3s1d/tweety/src/piezo.h

/*
 * piezo.h
 *
 *  Created on: Jul 30, 2016
 *      Author: sid
 */

#ifndef PIEZO_H_
#define PIEZO_H_

#define PIEZO_PIN		B,1

#define PIEZO_SINK_EEPROM	0
#define MINTONELENGTH		200

#define BEEP_ON			1
#define BEEP_OFF		0
#define BEEP_NOCHANGE		-1


/* 3.3mH coil -> tau = 79uS */
/* do not succeed 150uS (2tau) charge time */

/* charge time in uS */
#define PIEZO_VOL		((F_CPU/1000000UL) * 150)

extern uint8_t p_dosink;

void p_init(void);
void p_config(void);

/* control piezo, freq in Hz, approx. [100,3000], avoid 0 !! */
void p_set(uint16_t freq);
void p_off(void);

/* turn on/off signals */
void p_hello(void);
void p_bye(void);

void p_beep(uint8_t n);
void p_climb(void);

#endif /* PIEZO_H_ */
