3s1d/tweety/src/sleep.c

/*
 * sleep.c
 *
 *  Created on: Aug 2, 2016
 *      Author: sid
 */

#include <avr/io.h>
#include <avr/interrupt.h>
#include <avr/sleep.h>
#include <util/delay.h>

#include "flexport.h"
#include "battery.h"
#include "button.h"
#include "climb.h"
#include "piezo.h"
#include "sleep.h"

#include "debug.h"


ISR(PCINT2_vect)
{

}

void sleep(void)
{
	/* prepare system */
	climb_deinit();
	_delay_ms(250);

	p_bye();

	/* wait for button released */
	while(btn_pressed());

	/* configure button to trigger an PC interrupt (PCINT18 @ D,2) */
	PCMSK2 = _BV(PCINT18);
	PCICR = _BV(PCIE2);

	//uint8_t d = 10;
	//debug_put(&d, 1);

	set_sleep_mode(SLEEP_MODE_PWR_DOWN);
	uint8_t sleep = 1;
	while(sleep)
	{
		/* sleep */
		sleep_mode();

		/* switch de-bounce */
		_delay_ms(100);

		/* minimal button press time 1.5sec */
		uint8_t i;
		for(i=0; i<140; i++)
		{
			/* way too short */
			if(!btn_pressed())
			{
				i = 255;
				break;
			}
			_delay_ms(10);
		}
		if(i == 255)
			continue;

		//d = 13;
		//debug_put(&d, 1);

		/* quickly indicate we are up and running */
		//note: longer beeps confuses me...
		p_set(1000);
		_delay_ms(100);
		p_off();
		_delay_ms(100);

		for(i=0; i < 10; i++)
		{
			/* button released in time -> power on */
			if(!btn_pressed())
			{
				sleep = 0;
				break;
			}
			_delay_ms(100);
		}
	}

	//d = 11;
	//debug_put(&d, 1);

	/* disable PC int */
	PCICR = 0;

	/* indicate wakeup */
	p_hello();

	/* start up system again */
	climb_init();
}
